Kacman62/MoonBeam-Midi-Keyboard/PCBFiles/MoonBeam Midi Keyboard.kicad_sch

## KiCad design PCBFiles/MoonBeam Midi Keyboard.kicad_sch (2025-11-04)

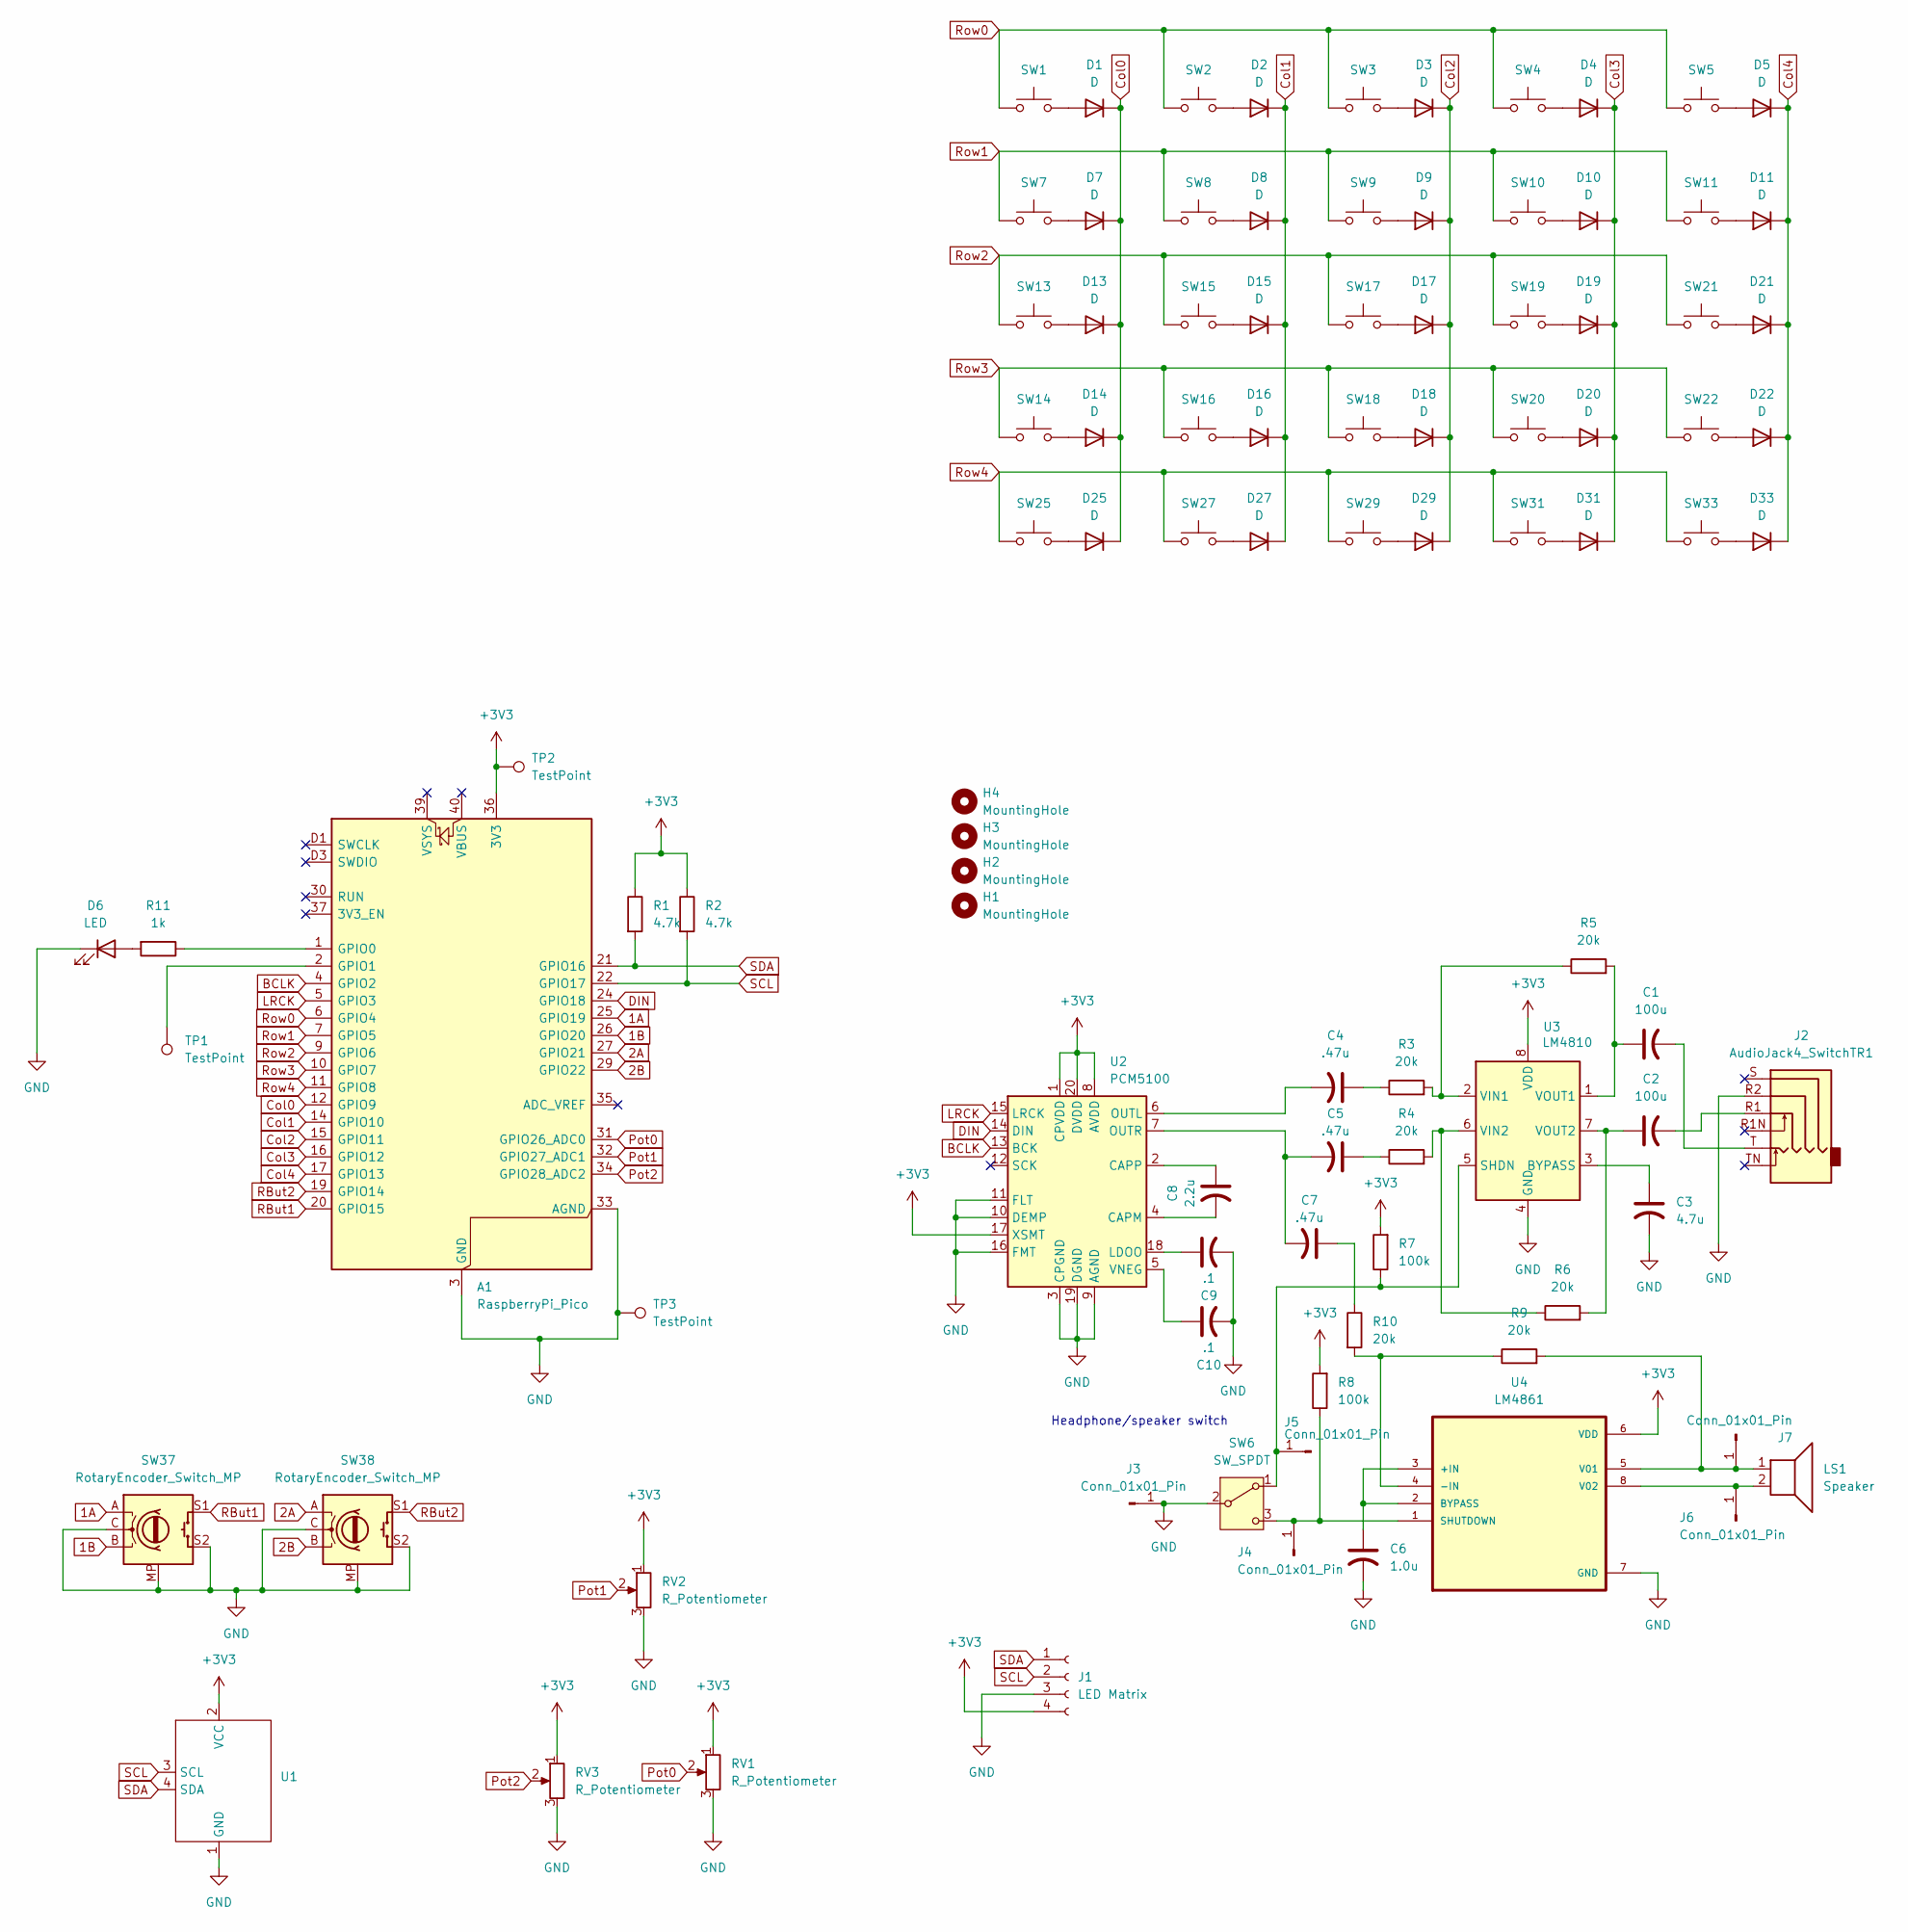
[picture p11: schematic MoonBeam Midi Keyboard.kicad_sch]

Parts:
A1: RaspberryPi_Pico; RaspberryPi_Pico_Common_THT
C1, C2: 100u; CP_Radial_D5.0mm_P2.50mm
C3: 4.7u; CP_Radial_D5.0mm_P2.50mm
C4, C5, C7: .47u; CP_Radial_D5.0mm_P2.50mm
C6: 1.0u; CP_Radial_D5.0mm_P2.50mm
C8: 2.2u; CP_Radial_D5.0mm_P2.50mm
C9, C10: .1; CP_Radial_D5.0mm_P2.50mm
D1, D2, D3, D4, D5, D7, D8, D9, D10, D11, D13, D14, D15, D16, D17, D18, D19, D20, D21, D22, D25, D27, D29, D31, D33: D; D_DO-35_SOD27_P7.62mm_Horizontal
D6: LED; LED_D3.0mm
H1, H2, H3: MountingHole; MountingHole_4.3mm_M4
H4: MountingHole; MountingHole_4.3mm_M4_DIN965
J1: LED Matrix; PinHeader_1x04_P2.54mm_Vertical
J2: AudioJack4_SwitchTR1; Jack_3.5mm_PJ31060-I_Horizontal
J3, J4, J5, J6, J7: Conn_01x01_Pin; TestPoint_Pad_4.0x4.0mm
LS1: Speaker
R1, R2: 4.7k; R_Axial_DIN0207_L6.3mm_D2.5mm_P7.62mm_Horizontal
R3, R4, R5, R6, R9, R10: 20k; R_Axial_DIN0207_L6.3mm_D2.5mm_P7.62mm_Horizontal
R7, R8: 100k; R_Axial_DIN0207_L6.3mm_D2.5mm_P7.62mm_Horizontal
R11: 1k; R_Axial_DIN0207_L6.3mm_D2.5mm_P7.62mm_Horizontal
RV1, RV2, RV3: R_Potentiometer; Slide Pot
SW1, SW2, SW3, SW4, SW5, SW7, SW8, SW9, SW10, SW11, SW13, SW14, SW15, SW16, SW17, SW18, SW19, SW20, SW21, SW22, SW25, SW27, SW29, SW31, SW33: SW_Omron_B3FS; SW_Cherry_MX_1.00u_PCB
SW6: SW_SPDT
SW37, SW38: RotaryEncoder_Switch_MP; RotaryEncoder_Alps_EC11E-Switch_Vertical_H20mm_MountingHoles
TP1, TP2, TP3: TestPoint; TestPoint_Pad_4.0x4.0mm
U1: 0.96 OLED I2C
U2: PCM5100; TSSOP-20_4.4x6.5mm_P0.65mm
U3: LM4810; TSSOP-8_3x3mm_P0.65mm
U4: LM4861; SOIC127P600X175-8N

Connections:
1A: A1.25 (GPIO19), SW37.A
1B: A1.26 (GPIO20), SW37.B
2A: A1.27 (GPIO21), SW38.A
2B: A1.29 (GPIO22), SW38.B
+3V3: A1.36 (3V3), J1.4, R1.1, R2.1, R7.2, R8.2, RV1.1, RV2.1, RV3.1, TP2.1, U1.2 (VCC), U2.1 (CPVDD), U2.8 (AVDD), U2.17 (XSMT), U2.20 (DVDD), U3.8 (VDD), U4.6 (VDD)
BCLK: A1.4 (GPIO2), U2.13 (BCK)
Col0: A1.12 (GPIO9), D1.1 (K), D7.1 (K), D13.1 (K), D14.1 (K), D25.1 (K)
Col1: A1.14 (GPIO10), D2.1 (K), D8.1 (K), D15.1 (K), D16.1 (K), D27.1 (K)
Col2: A1.15 (GPIO11), D3.1 (K), D9.1 (K), D17.1 (K), D18.1 (K), D29.1 (K)
Col3: A1.16 (GPIO12), D4.1 (K), D10.1 (K), D19.1 (K), D20.1 (K), D31.1 (K)
Col4: A1.17 (GPIO13), D5.1 (K), D11.1 (K), D21.1 (K), D22.1 (K), D33.1 (K)
DIN: A1.24 (GPIO18), U2.14 (DIN)
GND: A1.3 (GND), A1.8 (GND), A1.13 (GND), A1.18 (GND), A1.23 (GND), A1.28 (GND), A1.33 (AGND), A1.38 (GND), A1.D2 (GND), C3.2, C6.2, C9.2, C10.2, D6.1 (K), J1.3, J2.R2, J3.1, RV1.3, RV2.3, RV3.3, SW6.2 (B), SW37.C, SW37.MP, SW37.S2, SW38.C, SW38.MP, SW38.S2, TP3.1, U1.1 (GND), U2.3 (CPGND), U2.9 (AGND), U2.10 (DEMP), U2.11 (FLT), U2.16 (FMT), U2.19 (DGND), U3.4 (GND), U4.7 (GND)
LRCK: A1.5 (GPIO3), U2.15 (LRCK)
unnamed: A1.1 (GPIO0), R11.1
unnamed: A1.2 (GPIO1), TP1.1
unnamed: C1.1, R5.2, U3.1 (VOUT1)
unnamed: C1.2, J2.T
unnamed: C2.1, R6.2, U3.7 (VOUT2)
unnamed: C2.2, J2.R1
unnamed: C3.1, U3.3 (BYPASS)
unnamed: C4.1, R3.1
unnamed: C4.2, U2.6 (OUTL)
unnamed: C5.1, R4.1
unnamed: C5.2, C7.2, U2.7 (OUTR)
unnamed: C6.1, U4.2 (BYPASS), U4.3 (+IN)
unnamed: C7.1, R10.1
unnamed: C8.1, U2.2 (CAPP)
unnamed: C8.2, U2.4 (CAPM)
unnamed: C9.1, U2.18 (LDOO)
unnamed: C10.1, U2.5 (VNEG)
unnamed: D1.2 (A), SW1.2
unnamed: D2.2 (A), SW2.2
unnamed: D3.2 (A), SW3.2
unnamed: D4.2 (A), SW4.2
unnamed: D5.2 (A), SW5.2
unnamed: D6.2 (A), R11.2
unnamed: D7.2 (A), SW7.2
unnamed: D8.2 (A), SW8.2
unnamed: D9.2 (A), SW9.2
unnamed: D10.2 (A), SW10.2
unnamed: D11.2 (A), SW11.2
unnamed: D13.2 (A), SW13.2
unnamed: D14.2 (A), SW14.2
unnamed: D15.2 (A), SW15.2
unnamed: D16.2 (A), SW16.2
unnamed: D17.2 (A), SW17.2
unnamed: D18.2 (A), SW18.2
unnamed: D19.2 (A), SW19.2
unnamed: D20.2 (A), SW20.2
unnamed: D21.2 (A), SW21.2
unnamed: D22.2 (A), SW22.2
unnamed: D25.2 (A), SW25.2
unnamed: D27.2 (A), SW27.2
unnamed: D29.2 (A), SW29.2
unnamed: D31.2 (A), SW31.2
unnamed: D33.2 (A), SW33.2
unnamed: J4.1, R8.1, SW6.3 (C), U4.1 (SHUTDOWN)
unnamed: J5.1, R7.1, SW6.1 (A), U3.5 (SHDN)
unnamed: J6.1, LS1.2, U4.8 (V02)
unnamed: J7.1, LS1.1, R9.2, U4.5 (V01)
unnamed: R3.2, R5.1, U3.2 (VIN1)
unnamed: R4.2, R6.1, U3.6 (VIN2)
unnamed: R9.1, R10.2, U4.4 (-IN)
Pot0: A1.31 (GPIO26_ADC0), RV1.2
Pot1: A1.32 (GPIO27_ADC1), RV2.2
Pot2: A1.34 (GPIO28_ADC2), RV3.2
RBut1: A1.20 (GPIO15), SW37.S1
RBut2: A1.19 (GPIO14), SW38.S1
Row0: A1.6 (GPIO4), SW1.1, SW2.1, SW3.1, SW4.1, SW5.1
Row1: A1.7 (GPIO5), SW7.1, SW8.1, SW9.1, SW10.1, SW11.1
Row2: A1.9 (GPIO6), SW13.1, SW15.1, SW17.1, SW19.1, SW21.1
Row3: A1.10 (GPIO7), SW14.1, SW16.1, SW18.1, SW20.1, SW22.1
Row4: A1.11 (GPIO8), SW25.1, SW27.1, SW29.1, SW31.1, SW33.1
SCL: A1.22 (GPIO17), J1.2, R2.2, U1.3 (SCL)
SDA: A1.21 (GPIO16), J1.1, R1.2, U1.4 (SDA)

Notes on the sheet:
Headphone/speaker switch
